JJulio/AHRobot/Arduino/Utils/AHR_paint/GCODE.h

// This array is generated from a gcode file
// using a python code to extract coordinates 

/*
// Gode array in 1/10mm units
int gcode_index=0;
int gcode_lines=529; //529

int gcode[529][2]={
	{614,774},
	{628,764},
	{636,761},
	{654,759},
	{674,762},
	{683,767},
	{691,773},
	{698,781},
	{704,791},
	{712,814},
	{698,819},
	{692,801},
	{688,793},
	{676,781},
	{662,775},
	{643,775},
	{633,779},
	{625,785},
	{617,793},
	{612,804},
	{608,817},
	{605,832},
	{604,849},
	{606,872},
	{611,890},
	{618,904},
	{629,914},
	{641,920},
	{655,922},
	{669,920},
	{681,912},
	{690,900},
	{695,886},
	{710,890},
	{702,909},
	{690,925},
	{674,934},
	{661,937},
	{656,937},
	{638,935},
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
};

*/

// WANNA PLAY
// Gode array in 1/10mm units
int gcode_index=0;
int gcode_lines=358; 

int gcode[358][2]={
	{1637,677},
	{1653,677},
	{1654,693},
	{1657,705},
	{1663,715},
	{1687,744},
	{1694,756},
	{1698,768},
	{1699,781},
	{1698,792},
	{1695,803},
	{1691,812},
	{1684,821},
	{1676,828},
	{1667,832},
	{1653,836},
	{1646,836},
	{1635,835},
	{1626,833},
	{1617,828},
	{1609,822},
	{1603,814},
	{1598,803},
	{1592,779},
	{1609,777},
	{1613,795},
	{1621,809},
	{1633,817},
	{1646,820},
	{1660,817},
	{1671,808},
	{1679,795},
	{1682,779},
	{1679,762},
	{1644,717},
	{1639,702},
	{1637,678},
	{1636,650},
	{1636,625},
	{1655,625},
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
};
